KrogeChen/thermoMotorTester/sofrware/tester_ctrl/prj/app/app_cfg.h

#ifndef app_cfg_H
#define app_cfg_H

#include ".\snail_data_types.h"
#include ".\app_general.h"
#include ".\app_modbus.h"
#include ".\app_grating.h"
#include "..\.\pbc\pbc_sysTick\pbc_sysTick.h"
#include "..\.\mde\mde_sysClock\mde_system_clock.h"
#include "..\.\mde\mde_ledBlink\mde_ledBlink.h"
#include "..\.\mde\mde_mRtuSlave\mde_mRtuSlave.h"
#include "..\.\mde\mde_grating\mde_grating.h"

#endif //app_cfg_H
