KrogeChen/thermoMotorTester/sofrware/tester_ctrl/prj/mde/mde_grating/depend/bps_grating.h

//+++++++++++++++++++++++++++++++++++++++++++++++++++++++++++++++++++++++++++++
#ifndef bsp_grating_H
#define bsp_grating_H
//+++++++++++++++++++++++++++++++++++++++++++++++++++++++++++++++++++++++++++++
void bsp_gratingMeasure_cfg(viod);
sdt_bool bsp_pull_pulse_status(sdt_int8u* pulse_ABZ);
//+++++++++++++++++++++++++++++++++++++++++++++++++++++++++++++++++++++++++++++
#endif
