KrogeChen/thermoMotorTester/sofrware/tester_ctrl/prj/app/app_modbus.h

#ifndef app_modbus_H
#define app_modbus_H
//+++++++++++++++++++++++++++++++++++++++++++++++++++++++++++++++++++++++++++++
void app_modbus_task(void);
//+++++++++++++++++++++++++++++++++++++++++++++++++++++++++++++++++++++++++++++
#endif
