KrogeChen/thermoMotorTester/sofrware/tester_ctrl/prj/mde/mde_ledBlink/depend/bsp_ledBlink.h

//+++++++++++++++++++++++++++++++++++++++++++++++++++++++++++++++++++++++++++++
#ifndef bsp_ledBlink_H
#define bsp_ledBlink_H
//+++++++++++++++++++++++++++++++++++++++++++++++++++++++++++++++++++++++++++++
//
//-----------------------------------------------------------------------------
void bsp_lcd_runStatus_cfg(void);
void bsp_led_light(void);
void bsp_led_dark(void);
//+++++++++++++++++++++++++++++++++++++++++++++++++++++++++++++++++++++++++++++
#endif 
//+++++++++++++++++++++++++++++++++++++++++++++++++++++++++++++++++++++++++++++
